kennycoder/waku-ctl/src/globals.cpp

#include <numeric>
#include "globals.h"


// --- Global Variable Definitions ---

double a_currentTemperatures[ACTIVE_THERMISTORS_WITH_DELTAS];

// System State
unsigned long gHoldButtonCounter = 0;
bool b_TempAlarmStopped = true;
bool b_TempAlarmFiring = false;
bool b_RpmAlarmFiring = false;
bool b_ResetPressed = false;
bool b_BootCompleted = false;
Preferences systemPreferences;
ScreenView currentScreen = ScreenView::Overview;
String espChipIdStr = "AA:BB:CC:DD:EE"; // Updated during init

// Hardware Objects
Adafruit_SSD1306 oledDisplay(SCREEN_WIDTH, SCREEN_HEIGHT, &Wire, PIN_OLED_RESET);
AsyncWebServer webServer(80);
DNSServer dnsServer;
WiFiClient wifiClient;
PubSubClient mqttClient(wifiClient);
Adafruit_ADS1115 ads;
USBCDC USBTelemetryPort;

// WiFi / AP
const IPAddress AP_LOCAL_IP(192, 168, 4, 1);
const IPAddress AP_GATEWAY_IP(192, 168, 4, 1);
const IPAddress AP_SUBNET_MASK(255, 255, 255, 0);
const String AP_LOCAL_URL = "http://192.168.4.1";

// Settings & Config
Settings systemSettings;
std::map<int, TemperatureSensorSettings> m_SensorSettings;
std::map<int, LedSettings> m_LedSettings;

// LED Data
CRGB a_LedBuffers[ACTIVE_LED_STRIPS][MAX_LEDS_PER_STRIP];

// Thermistor/Fan IDs
std::vector<int> a_ThermistorIds;
std::vector<String> a_FanNames;

// Fan State
unsigned long a_CurrentFanSpeedsRpm[ACTIVE_FANS] = {999, 999, 999, 999};

std::map<int, FanRpmTarget> m_TargetFanRpm;
std::map<int, double> m_PidOutputs;
std::map<int, int> m_CurrentFanPwmValues;

// std::map<int, FanPinPair> PIN_FAN_MAP = {
//     {0, {14, 13}},
//     {1, {12, 11}},
//     {2, {10, 9}},
//     {3, {7, 6}}
// };

// New Board pin layout

std::map<int, FanPinPair> PIN_FAN_MAP = {
    {0, {10, 14}},
    {1, {11, 21}},
    {2, {12, 47}},
    {3, {13, 48}}
};


unsigned long lastTach = 0;

// Fan ISR Pulse Counters
volatile unsigned long fan0_pulses = 0;
volatile unsigned long fan0_last_pulse_micros = 0;
volatile unsigned long fan1_pulses = 0;
volatile unsigned long fan1_last_pulse_micros = 0;
volatile unsigned long fan2_pulses = 0;
volatile unsigned long fan2_last_pulse_micros = 0;
volatile unsigned long fan3_pulses = 0;
volatile unsigned long fan3_last_pulse_micros = 0;

// Fan RPM Calculation Timestamps
unsigned long fan0_last_calc_time = 0;
unsigned long fan1_last_calc_time = 0;
unsigned long fan2_last_calc_time = 0;
unsigned long fan3_last_calc_time = 0;

void init_globals() {
    a_ThermistorIds.resize(ACTIVE_THERMISTORS);
    std::iota(a_ThermistorIds.begin(), a_ThermistorIds.end(), 0);

    a_FanNames.resize(ACTIVE_FANS);
    if (ACTIVE_FANS > 0) {
        a_FanNames[0] = "PUMP";
        for (int i = 1; i < ACTIVE_FANS; ++i) {
            a_FanNames[i] = String(i);
        }
        for (int i = 0; i < ACTIVE_FANS; ++i) {
            m_TargetFanRpm[i] = {0, 0, 0, 0, false};
        }
    }
}
