kennycoder/waku-ctl/src/globals.h

#ifndef GLOBALS_H
#define GLOBALS_H

#define NO_ADAFRUIT_SSD1306_COLOR_COMPATIBILITY

#include <map>
#include <vector>
#include <stdint.h>
#include <Arduino.h>
#include <Preferences.h>
#include <SPI.h>
#include <Wire.h>
#include <WiFi.h>
#include <FS.h>
#include <LittleFS.h>
#include <esp_sntp.h>
#include <AsyncTCP.h>
#include <DNSServer.h>
#include <PubSubClient.h>
#include <Adafruit_GFX.h>
#include <Adafruit_SSD1306.h>
#include "FastLED.h"
#include "ArduinoJson.h"
#include "ESPAsyncWebServer.h"
#include <Adafruit_ADS1X15.h>
#include "USB.h"
#include "USBCDC.h"

#include "types.h"
#include "config_constants.h"
#include "pins.h"

// --- Global Variables ---
extern double a_currentTemperatures[ACTIVE_THERMISTORS_WITH_DELTAS];

// System State
extern unsigned long gHoldButtonCounter;
extern bool b_TempAlarmStopped;
extern bool b_TempAlarmFiring;
extern bool b_RpmAlarmFiring;
extern bool b_ResetPressed;
extern bool b_BootCompleted;
extern ScreenView currentScreen;
extern String espChipIdStr;

// Global Objects
extern AsyncWebServer webServer;
extern DNSServer dnsServer;
extern WiFiClient wifiClient;
extern PubSubClient mqttClient;
extern Preferences systemPreferences;

// Hardware Objects
extern Adafruit_SSD1306 oledDisplay;
extern Adafruit_ADS1115 ads;
extern USBCDC USBTelemetryPort;

// WiFi / AP
extern const IPAddress AP_LOCAL_IP;
extern const IPAddress AP_GATEWAY_IP;
extern const IPAddress AP_SUBNET_MASK;
extern const String AP_LOCAL_URL;

// Settings & Config
extern Settings systemSettings;
extern std::map<int, TemperatureSensorSettings> m_SensorSettings;
extern std::map<int, LedSettings> m_LedSettings;
// LED Data
extern CRGB a_LedBuffers[ACTIVE_LED_STRIPS][MAX_LEDS_PER_STRIP];

// Thermistor/Fan IDs
extern std::vector<int> a_ThermistorIds;
extern std::vector<String> a_FanNames;

// Fan State
extern unsigned long a_CurrentFanSpeedsRpm[ACTIVE_FANS];
extern std::map<int, FanRpmTarget> m_TargetFanRpm;
extern std::map<int, double> m_PidOutputs;
extern std::map<int, int> m_CurrentFanPwmValues;

extern unsigned long lastTach;

// Fan ISR Pulse Counters (MUST be volatile)
extern volatile unsigned long fan0_pulses;
extern volatile unsigned long fan0_last_pulse_micros;
extern volatile unsigned long fan1_pulses;
extern volatile unsigned long fan1_last_pulse_micros;
extern volatile unsigned long fan2_pulses;
extern volatile unsigned long fan2_last_pulse_micros;
extern volatile unsigned long fan3_pulses;
extern volatile unsigned long fan3_last_pulse_micros;

// Fan RPM Calculation Timestamps
extern unsigned long fan0_last_calc_time;
extern unsigned long fan1_last_calc_time;
extern unsigned long fan2_last_calc_time;
extern unsigned long fan3_last_calc_time;

void init_globals();

#endif // GLOBALS_H
